pianic2/homeedge-ai-platform/docs/evidence/IHAP-52/summaries/README.md

# IHAP-52 Sanitized Validation Summaries

This directory is reserved for reviewed aggregate summaries generated from central-node validation runs.

Raw harness output under `tools/hardware-validation/ihap-52-central-node/runs/` remains local and ignored by Git.

A public summary may be added only after checking that it does not expose Wi-Fi credentials, SSIDs, MAC addresses, private IP addresses, hostnames, usernames or unnecessary local paths.

A summary may report:

- device family/model;
- architecture, logical CPU count and RAM capacity;
- storage capacity and microSD application class;
- Wi-Fi gate pass/fail without private addressing;
- PSU electrical rating and pass/fail disposition;
- temperature aggregates and throttling/undervoltage flags;
- stress duration and worker result;
- overall automated gate;
- manual cooling/enclosure configuration;
- explicit `[UNVALIDATED]` boundaries.

The 2026-09-05 pre-flight is not yet a publishable final validation summary because the full stress phase did not execute. It is retained as task evidence in the IHAP-52 evidence index and Jira.

A passing summary supports only the declared IHAP-52 validation envelope. It does not prove production readiness, final application sizing, microSD endurance/retention or AI acceleration.
