pianic2/homeedge-ai-platform/docs/product/product-vision.md

# Product Vision, MVP Boundaries and Glossary

**Issue:** IHAP-11 — S0-002 — Product Vision, MVP Boundaries and Glossary  
**Project:** [ITS] [EDGE] HomeEdge AI Platform  
**Document type:** Product foundation / governance documentation  
**Status:** Active product foundation — updated through accepted ADRs  
**Last controlled MVP update:** 2026-08-31 — ADR-0004 Local Status Display  
**Source of truth:** This versioned GitHub document is the technical source of truth for the Product Vision, MVP boundaries, and initial glossary until superseded by a later reviewed change.

<!--
AI_AGENT_METADATA:
  issue: IHAP-11
  related_issues:
    - IHAP-15
    - IHAP-53
  document_type: product_foundation
  source_of_truth: github_versioned_documentation
  task_scope: documentation_governance_only
  runtime_changes_allowed: false
  firmware_changes_allowed: false
  backend_changes_allowed: false
  mobile_changes_allowed: false
  production_ready_claims_allowed: false
  unvalidated_claim_marker: "[UNVALIDATED]"
  mvp_firmware_node: "firmware/room-env-node/"
  mvp_node_semantics: "generic_room_door_node"
  mvp_physical_positioning: "near_room_door"
  mvp_includes:
    - temperature_collection
    - humidity_collection
    - local_presence_detection
    - door_open_closed_state
    - local_status_display
    - http_json_event_direction
    - minimal_event_schema_direction
    - documentation_governance
  accepted_local_display_adr: ADR-0004
  local_display_runtime_integration_status: unvalidated_until_final_room_node_implementation
  mvp_excludes:
    - raw_audio_collection
    - individual_presence_tracking
    - behavioral_history_tracking
    - person_identification
    - window_sensor_scope
    - 220v_automation
    - esp32_direct_kafka_producer
    - production_grade_security_certification
    - commercial_claims
    - safety_critical_claims
  service_boundaries_target_only:
    - services/ingestion/
    - services/device-registry/
    - services/read-model/
    - services/ai-insight/
  data_classification_boundary:
    canonical_section: "4.4 Data Classification and Privacy Boundaries"
    mvp_data:
      - temperature
      - humidity
      - local_non_identifying_presence_state
      - door_open_closed_telemetry
    technical_metadata:
      - timestamp
      - device_node_id
      - room_id
      - firmware_version
      - ip_network_metadata
    future_or_out_of_mvp:
      - window_sensor_scope
      - advanced_presence_analytics
    blocked_data:
      - raw_audio
      - person_identification
      - individual_presence_tracking
      - behavioral_history
      - routine_profiling
    stakeholder_exposure:
      raw_audio: blocked
      identity_data: blocked
      behavioral_history: blocked
      private_network_metadata: redact_or_omit
      door_state: telemetry_only
      presence_state: local_non_identifying_only
  review_policy:
    - do_not_close_jira_without_project_owner_approval
    - keep_mvp_future_out_of_mvp_target_distinction
    - do_not_overstate_runtime_maturity

HIDDEN_ANTI_REGRESSION_RULES:
  - This document must not contradict the repository skeleton introduced by IHAP-10.
  - The only firmware node in the MVP is firmware/room-env-node/.
  - firmware/room-env-node/ represents the first generic room/door node positioned near the room door.
  - The MVP includes temperature, humidity, local non-identifying presence detection, door open/closed state, and the local status display capability accepted by ADR-0004.
  - ADR-0004 does not imply that final room-node display firmware, final pinout, quantitative power, enclosure mechanics or BOM propagation are already complete.
  - The local display is read-only, compact status/debug UI; do not turn it into a terminal, touch UI, identity/history surface, or alarm/security interface.
  - No dedicated status LED is an MVP requirement when the accepted local display provides local status indication.
  - The four backend directories remain target service boundaries, not proof of completed production services.
  - Kafka direct production from ESP32 remains OUT OF MVP.
  - Backend-side Kafka/event streaming remains FUTURE unless a later ADR and implementation task validate it.
  - Raw audio collection remains OUT OF MVP.
  - Local, non-identifying presence detection is allowed inside the MVP.
  - Individual presence tracking, behavioral history, identity inference, and routine profiling remain OUT OF MVP.
  - Door open/closed state is allowed inside the MVP as telemetry only.
  - Door state must not be presented as certified access control, alarm-grade intrusion detection, or safety-critical security evidence.
  - Window sensors remain FUTURE and OUT OF MVP unless changed by ADR.
  - 220V automation remains OUT OF MVP.
  - Mobile monitoring is a target direction unless supported by implementation evidence.
  - AI insight is a target/future service boundary unless supported by implementation evidence.
  - Stakeholder reports must not contain sensitive data, raw personal telemetry, raw audio, behavioral tracking, or unsupported production/safety/commercial claims.
  - Any unproven claim must be marked as [UNVALIDATED].
  - Documentation must distinguish clearly between MVP, FUTURE, OUT OF MVP, and TARGET.
  - Jira must track status, evidence, decisions, and review state.
  - GitHub must remain the source of truth for versioned technical documentation.

HIDDEN_EVIDENCE_EXPECTATIONS:
  - A GitHub branch dedicated to the active task.
  - A pull request linked to the active Jira issue.
  - This versioned document under docs/product/product-vision.md.
  - A Jira comment linking the PR and summarizing the documentation scope.
  - Jira status moved to review after PR creation or Project Owner instruction.
  - No transition to completed until explicit project owner approval.
-->

---

## 1. Product Snapshot

HomeEdge AI Platform is an educational, portfolio-grade smart home platform built around a first edge node, backend service boundaries, mobile monitoring, and source-of-truth documentation.

The first MVP node is a **generic room/door node** positioned near the room door.

The MVP focuses on a small, reviewable smart home vertical slice:

- room temperature;
- room humidity;
- local non-identifying presence detection;
- room door open/closed state;
- a compact read-only local status display for user/maintenance visibility, accepted by ADR-0004;
- HTTP/JSON event direction toward ingestion;
- documented backend service boundaries;
- governance through GitHub and Jira.

The local display capability is part of the MVP product boundary. The tested 0.96-inch-class 128×64 monochrome I2C profile and owned specimen evidence are defined by ADR-0004. Final integration into `firmware/room-env-node/`, final pins, quantitative power behavior, enclosure mechanics and definitive BOM propagation remain separate work and must not be inferred from this Product Vision update.

The MVP does **not** include person tracking, behavioral history, raw audio collection, certified access control, alarm-grade intrusion detection, 220V automation, or direct Kafka production from ESP32.

---

## 2. Document Control

This document defines the product framing for HomeEdge AI Platform and is updated by reviewed Product Owner decisions and accepted ADRs.

It is intentionally limited to product documentation and governance. It does **not** introduce firmware, backend, mobile, infrastructure, CI/CD, cloud, Kafka, AI runtime, or production implementation by itself.

### 2.1 Scope of this document

Included:

- Product Vision.
- MVP boundaries.
- FUTURE scope.
- OUT OF MVP scope.
- Initial glossary.

Excluded:

- Runtime implementation.
- Firmware implementation changes.
- Backend service implementation.
- Mobile app implementation.
- Production-readiness claims.
- Safety-critical claims.
- Commercial claims.

### 2.2 Claim policy

Any capability that is not implemented, tested, and supported by runtime evidence must be marked as `[UNVALIDATED]`.

An accepted architectural/product requirement may be part of the MVP boundary before final runtime integration, but its implementation maturity must remain explicit. ADR-0004 therefore accepts the local-display capability/profile while final room-node integration remains `[UNVALIDATED]` until implementation evidence exists.

A statement may describe a **TARGET** architecture only when it is explicitly framed as target, planned, or future work.

---

## 3. Product Vision

### 3.1 What HomeEdge AI Platform is

HomeEdge AI Platform is an educational, portfolio-grade smart home platform that connects edge devices, backend services, mobile monitoring, structured documentation, and an AI-ready insight layer.

The platform is designed around an edge-first architecture:

```text
Edge Nodes -> Backend Services -> Mobile Dashboard -> AI-ready Insights
```

At Sprint 0, this is a product and architecture direction, not proof that all runtime components already exist.

### 3.2 Why it exists

HomeEdge exists to create a coherent end-to-end engineering project suitable for the ITS context and for a technical portfolio.

The project connects multiple disciplines in one traceable system:

- embedded firmware on ESP32-class devices;
- sensor-based smart home telemetry;
- compact local device status/debug visibility;
- HTTP/JSON event ingestion;
- backend service boundaries;
- mobile-first monitoring;
- documentation as source of truth;
- governance through Jira, GitHub, and review evidence;
- AI-ready data interpretation as a later architectural target.

### 3.3 Problem it solves

HomeEdge addresses the problem of building a smart home system in a controlled, incremental, and reviewable way.

Instead of starting from a broad and ambiguous smart home vision, the project narrows the first vertical slice to a single generic room/door node and a minimal telemetry flow.

The project solves these early engineering problems:

- making hardware, firmware, backend, mobile, and documentation boundaries explicit;
- preventing uncontrolled scope expansion;
- avoiding unverified production-ready claims;
- keeping stakeholder visibility high;
- documenting what is implemented, what is targeted, and what is explicitly out of scope;
- creating a project structure that can scale without hiding current maturity.

### 3.4 Educational and portfolio value

HomeEdge is valuable as a learning and portfolio project because it demonstrates how to model a real platform from the beginning, not only how to write isolated code.

It shows:

- product thinking;
- architectural decomposition;
- embedded-to-cloud reasoning;
- source-of-truth documentation;
- issue-driven delivery;
- pull-request evidence;
- anti-regression governance;
- explicit MVP scoping;
- clear distinction between implemented features and target architecture.

This makes the project readable for ITS stakeholders, reviewers, recruiters, and future collaborators.

### 3.5 Technical value

HomeEdge is technically valuable because it is structured as a scalable platform rather than a single prototype script.

The main technical axes are:

- **Edge devices:** ESP32-class nodes collecting room-level signals and exposing a compact local status/debug surface.
- **Backend services:** target service boundaries for ingestion, device registry, read model, and AI insight.
- **Mobile monitoring:** mobile-first dashboard direction for telemetry and device health visibility.
- **AI-ready insight layer:** future service boundary for deriving insights from validated data.
- **Governance:** Jira for workflow and evidence, GitHub for versioned technical source of truth, and PR reviews for change validation.

At Sprint 0, these axes define direction and boundaries. They do not imply that every component is implemented.

---

## 4. MVP Boundaries

### 4.1 MVP definition

The MVP is the smallest reviewable vertical slice of HomeEdge.

It must prove the platform direction without expanding into high-risk or unvalidated smart home automation features.

The MVP is centered on one firmware node:

```text
firmware/room-env-node/
```

This node is the first generic room/door node of the smart home platform. It is assumed to be positioned near the room door and is responsible for collecting minimal room-level signals.

In the MVP, the node may collect:

- temperature;
- humidity;
- local non-identifying presence state;
- door open/closed state.

The MVP node also includes a **compact read-only local status display capability** accepted by ADR-0004. The accepted display profile is 0.96-inch-class, 128×64, monochrome OLED over I2C. Final room-node rendering/driver integration remains `[UNVALIDATED]` until implemented and tested outside the IHAP-53 validation harness.

No other firmware node is part of the MVP unless a later ADR explicitly changes this boundary.

### 4.2 MVP included

The MVP includes the following scope:

| Area | MVP scope | Status framing |
|---|---|---|
| Firmware node | One generic Room/Door Environment Node under `firmware/room-env-node/` | MVP |
| Physical placement | Node positioned near the room door | MVP assumption |
| Environment telemetry | Temperature and humidity collection | MVP |
| Local presence | Local presence detection as a boolean or state signal, without identity, behavioral history, or individual tracking | MVP |
| Door state | Door open/closed state detection | MVP |
| Local status display | Compact read-only 0.96-inch-class 128×64 monochrome I2C status/debug display; healthy UI shows room label, temperature, humidity, presence and door state; no dedicated status LED requirement | MVP capability accepted by ADR-0004; final room-node firmware/pinout/power/enclosure integration remains `[UNVALIDATED]` |
| Transport | HTTP/JSON event sent toward ingestion backend | MVP target until implemented and verified |
| Event model | Minimal event schema for room environment, presence state, and door state | MVP target until implemented and verified |
| Backend | Ingestion boundary as target service area | TARGET |
| Device registry | Device identity/metadata boundary as target service area | TARGET |
| Read model | Query/read-oriented boundary as target service area | TARGET |
| AI insight | AI-ready insight boundary as target service area | TARGET / FUTURE |
| Mobile dashboard | Mobile monitoring documented as target | TARGET |
| Documentation | GitHub versioned documentation as source of truth | MVP governance |
| Jira governance | Jira comments/status/evidence for task tracking | MVP governance |

Presence detection in the MVP means detecting whether presence is currently observed in a room-level context.

Presence detection does **not** mean tracking people, identifying people, storing behavioral history, profiling routines, or producing safety-critical occupancy guarantees.

Door state detection in the MVP means detecting whether the room door is open or closed.

Door state detection does **not** mean access control, intrusion certification, alarm-grade security, or safety-critical monitoring.

The local display may present only current permitted room-level status and compact maintenance diagnostics. It must not expose identity, behavioral/occupancy history, credentials, SSID, access-control/alarm semantics or other data outside the accepted privacy boundary.

### 4.3 Minimal event direction

The MVP event direction is HTTP/JSON from `room-env-node` toward an ingestion backend.

A minimal room environment event may include fields such as:

```json
{
  "event_type": "room.environment.sampled",
  "device_id": "room-env-01",
  "timestamp": "2026-07-07T00:00:00Z",
  "temperature_c": 24.5,
  "humidity_percent": 55.0,
  "presence_detected": false,
  "door_open": false,
  "firmware_version": "0.0.0-unvalidated"
}
```

This schema is directional and must remain `[UNVALIDATED]` until the schema is formally versioned, implemented, and tested.

The `presence_detected` field represents a local, non-identifying room-level state. It must not be interpreted as identity, person tracking, behavioral profiling, or safety-critical occupancy evidence.

The `door_open` field represents the local open/closed state of the room door. It must not be interpreted as certified access control, intrusion detection, or safety-critical security evidence.

### 4.4 Data Classification and Privacy Boundaries

The MVP uses minimal room-level telemetry. Data must stay classified by purpose, privacy boundary, and stakeholder exposure.

| Data / signal | Classification | MVP status | Privacy boundary | Stakeholder exposure |
|---|---|---|---|---|
| Temperature | Room telemetry | MVP | Non-identifying room-level signal. | Show allowed. |
| Humidity | Room telemetry | MVP | Non-identifying room-level signal. | Show allowed. |
| Presence detected | Local state telemetry | MVP | Local, non-identifying state only; no identity, individual tracking, behavioral history, or routine profiling. | Show only as generic room state. |
| Door open/closed | Local state telemetry | MVP | Telemetry only; not access control, antifurto, alarm-grade, safety-critical, or security-certified evidence. | Show only as telemetry. |
| Timestamp | Technical metadata | MVP / TARGET depending on schema evidence | Can support inference if retained, correlated, or shown with other signals. | Show only when needed; redact or aggregate where appropriate. |
| Device/node id | Technical metadata | MVP / TARGET depending on schema evidence | Must not expose sensitive domestic topology or private installation details. | Redact or omit unless required for review. |
| Room id | Technical metadata | MVP / TARGET depending on schema evidence | Must remain generic; no private address or precise domestic location. | Generic labels only. |
| Firmware version | Technical metadata | MVP / TARGET depending on schema evidence | Useful for evidence, but not a privacy or security guarantee. | Show allowed when useful. |
| IP/network metadata | Technical metadata | OUT of stakeholder view | Sensitive domestic/infrastructure detail. | Redact or omit. |
| Raw audio | Sensitive raw signal | OUT OF MVP | Not collected in MVP. | Blocked. |
| Person identification | Identity data | OUT OF MVP | Not allowed. | Blocked. |
| Individual presence tracking | Behavioral or identity-linked data | OUT OF MVP | Not allowed. | Blocked. |
| Behavioral history / routine profiling | Behavioral data | OUT OF MVP | Not allowed. | Blocked. |
| Window sensors | Opening telemetry | FUTURE / OUT OF current MVP | Not part of the current room/door node scope. | Do not imply MVP delivery. |

The accepted local display does not create a new class of telemetry. It may expose only current values/states permitted by this table plus compact maintenance diagnostics allowed by ADR-0004. Normal display content must omit SSID, credentials and behavioral history; private network metadata remains excluded from ordinary stakeholder/user display.

The table does not validate runtime behavior. Event fields, service boundaries, mobile views, AI insight, storage behavior, and final room-node display integration remain `[UNVALIDATED]` until implementation and test evidence exist.

### 4.5 MVP acceptance boundary

The MVP must remain understandable without requiring any of the following:

- multiple hardware node types;
- raw audio collection;
- individual presence tracking;
- behavioral presence history;
- person identification;
- window detection;
- certified access control;
- alarm-grade intrusion detection;
- 220V automation;
- direct Kafka production from ESP32;
- cloud deployment;
- production-grade security certification;
- commercial or safety-critical positioning.

The accepted local status display is part of the MVP and is therefore not an optional FUTURE feature. Its presence must not be used to imply final firmware integration, production maturity, quantitative autonomy, certified enclosure suitability or security/alarm semantics.

---

## 5. FUTURE Scope

The following items are intentionally future scope. They may be explored later only through explicit tasks, ADRs, risk assessments, and review evidence.

| Area | FUTURE item | Notes |
|---|---|---|
| Presence | Advanced presence radar features | Basic local presence detection is MVP; identity, tracking, behavioral history, room-to-room movement analysis, and advanced presence analytics are not MVP. |
| Openings | Window sensors and multi-opening topology | Door open/closed state for the first room/door node is MVP; window sensors and multi-opening modeling are FUTURE. |
| Audio-derived signals | Noise detection derived from local processing | Raw audio collection remains OUT OF MVP. |
| Automation | Smart home automations | Requires safety and risk review. |
| AI | Advanced AI insight generation | Requires validated data and clear privacy boundaries. |
| Event streaming | Kafka on backend/event streaming side | Backend-side target only, not ESP32 direct producer in MVP. |
| DevOps | More complete CI/CD | Future hardening task. |
| Deployment | Cloud deployment | Future deployment milestone. |
| Mobile | Full mobile dashboard implementation | Target beyond initial documentation unless separately implemented. |

FUTURE means planned or possible later work. It does not mean implemented.

---

## 6. OUT OF MVP Scope

The following items are explicitly out of the MVP and must not be implied as delivered by Sprint 0 documentation.

| Item | Reason |
|---|---|
| Raw audio collection | Privacy risk and not needed for the first telemetry vertical slice. |
| Individual presence tracking | OUT OF MVP. The MVP may detect local presence state, but must not identify people, track individuals, store behavioral history, or profile routines. |
| Behavioral presence history | OUT OF MVP. Presence events must not become a person-level movement log or routine inference system in the MVP. |
| Window sensors in MVP | OUT OF MVP. The first MVP node may detect the room door open/closed state, but window sensors are future scope. |
| Certified access control | OUT OF MVP. Door open/closed state is telemetry only, not an access-control or alarm-grade security feature. |
| Alarm-grade intrusion detection | OUT OF MVP. Door state and presence state must not be presented as certified intrusion detection. |
| 220V automation | Safety risk and requires dedicated electrical/security review. |
| Production-grade security/certification | Not implemented or verified in Sprint 0. |
| Kafka client directly on ESP32 | Too heavy and outside the MVP boundary; backend event streaming may be future scope. |
| Commercial claims | Project is educational/portfolio-oriented unless later validated otherwise. |
| Safety-critical claims | No safety-critical guarantees are provided. |
| Full AI automation | AI insight is a target boundary, not a validated runtime capability in Sprint 0. |

---

## 7. Target Service Boundaries

The repository skeleton defines four backend service boundaries:

```text
services/ingestion/
services/device-registry/
services/read-model/
services/ai-insight/
```

These are **target service boundaries**.

They do not prove that production-ready services exist. They define where backend responsibilities should be modeled as the platform evolves.

### 7.1 Ingestion boundary

The ingestion boundary is responsible for receiving, validating, and accepting telemetry events from edge nodes.

At Sprint 0, this is a target boundary unless implementation evidence exists in a later task.

### 7.2 Device Registry boundary

The device registry boundary is responsible for device identity, metadata, and lifecycle state.

At Sprint 0, this is a target boundary unless implementation evidence exists in a later task.

### 7.3 Read Model boundary

The read model boundary is responsible for query-oriented representations of data used by dashboards, APIs, or monitoring views.

At Sprint 0, this is a target boundary unless implementation evidence exists in a later task.

### 7.4 AI Insight boundary

The AI insight boundary is responsible for future interpretation, classification, summarization, anomaly detection, or insight generation from validated data.

At Sprint 0, this is a target/future boundary, not a validated AI runtime.

---

## 8. Glossary

| Term | Definition |
|---|---|
| Edge Node | A physical embedded device near the environment being observed. In this project, edge nodes are expected to use ESP32-class hardware unless changed by ADR. |
| Generic Room/Door Node | The first MVP smart home node placed near a room door. It collects minimal room environment data, local presence state, door open/closed state, and includes the accepted local status display capability. |
| Room Environment Node | The MVP firmware node located at `firmware/room-env-node/`. In the MVP, it acts as a generic room/door node responsible for temperature, humidity, local presence detection, door open/closed state, and the local status display capability accepted by ADR-0004. |
| Local Status Display | The read-only compact status/debug display accepted by ADR-0004 for the reference MVP node. Reference profile: 0.96-inch-class, 128×64, monochrome OLED, I2C. Final product pinout, power policy, enclosure and definitive BOM remain separate follow-up work. |
| Event | A structured record describing something observed or produced by the system, such as a room environment sample. |
| Door State | A local telemetry signal indicating whether the room door is open or closed. It is allowed in the MVP as a non-certified state signal. |
| Presence Detection | A local, non-identifying room-level signal indicating whether presence is currently detected. It is allowed in the MVP only as a minimal state signal. |
| Presence Tracking | Person-level, historical, behavioral, or identity-linked tracking of presence over time. This is OUT OF MVP. |
| Ingestion | The backend boundary responsible for receiving and validating incoming events. |
| Device Registry | The backend boundary responsible for device identity, metadata, ownership, lifecycle, and known-device state. |
| Read Model | A query-optimized representation of data used by dashboards, APIs, or monitoring views. |
| AI Insight | A future or target capability that derives higher-level interpretation from validated data. It is not a Sprint 0 runtime claim. |
| Source of Truth | The authoritative place where a technical decision, boundary, or project fact is maintained. For versioned technical documentation, this is GitHub unless explicitly superseded. |
| ADR | Architecture Decision Record. A reviewed document that captures an architectural decision, context, consequences, and alternatives. |
| MVP | Minimum Viable Product. The smallest coherent and reviewable vertical slice of the platform. |
| FUTURE | A planned or possible later capability. It is not implemented unless separate evidence proves it. |
| OUT OF MVP | Explicitly excluded from the current MVP scope. These items must not be implied as delivered. |
| TARGET | A documented architectural direction or service boundary. It is not proof of implementation. |
| `[UNVALIDATED]` | Marker for a claim, capability, schema, flow, or assumption that has not yet been implemented, tested, and supported by runtime evidence. |
| Stakeholder Report | A concise status report for stakeholders, such as ITS professors, that communicates progress, risks, evidence, and next steps without leaking sensitive data or making unsupported claims. |
| Runtime Evidence | Concrete evidence from running software or hardware, such as logs, tests, screenshots, traces, build outputs, or verified API responses. |
