pianic2/homeedge-ai-platform/docs/evidence/IHAP-55/review-summary.md

# IHAP-55 pre-fabrication review checkpoint — 2026-09-13

**Readiness: HOLD.** This is a technical checkpoint in existing branch `ihap-55-integrated-modular-edge-pcb` and draft PR #37, not a fabrication or reference-implementation approval.

The 2026-09-12 review compared the accepted ADR-0001/0002/0003/0004/0005/0007 and IHAP-50 connection matrix with the revision-A JSON contract and copied firmware. GPIO0/1/3/4/5/6/7/10, USB GPIO18/19, reserved strapping GPIO2/8/9, optional UART0 GPIO20/21, connector logical pin order, DHT11/BME280 alternatives, radar receive-only 256000 baud and MC-38 10 kΩ/1 kΩ/DNP 100 nF remain represented. No audio GPIO, ADC, connector or power allocation was added. The IHAP-50 firmware main source was identical before the IHAP-55 ADC/command additions; the existing integrated sample stream was retained.

Software gate evidence: 28/28 behavioral cases and 12/12 host tests passed; ESP-IDF v6.0.1 compiled the ESP32-C3/4 MB/USB Serial-JTAG firmware. The TLA2024 four-channel path is initialized, read, range-checked and serialized in the command response, but has no physical-board validation.

The existing PR #37 was updated to commit `2926a9019cbc9f0fd4081286352928bc6102162e` on 2026-09-13. [GitHub Actions run 34757325971](https://github.com/pianic2/homeedge-ai-platform/actions/runs/34757325971) completed successfully: `contract-and-host` passed; `kicad-erc-drc` job completed but explicitly skipped KiCad installation, ERC and DRC because neither EDA source exists. This is CI software-gate success, **not** an ERC/DRC PASS. Later evidence commits require a fresh CI check at their own HEAD.

Two technical failures prevent an EDA/fabrication-ready claim: (1) the passive board-health ADC dividers can drive AIN above VDD+0.3 V while SYS_3V3 is absent; (2) the vendor PSpice experiments under ngspice 44.2 did not produce plausible output voltages, so no switching model validates dynamic rail performance. MP2636 protection/NTC, reverse-cell prevention, exact passives and module pull-ups are additional open circuit items. No native schematic/PCB, ERC, preliminary envelope or DRC exists at this checkpoint.

The Accepted ADR-0007 baseline remains unchanged. IHAP-56's `RT-R012-01` and `RT-R013-01` remain Proposed/Pending Evidence. No procurement, fabrication or merge was performed. Project Owner gates are deferred until a technically reviewable board and IHAP-51 mechanical feedback exist.
