pianic2/homeedge-ai-platform/docs/evidence/IHAP-49/ihap-56-post-merge-reconciliation.md

# IHAP-56 Post-Merge Lifecycle Reconciliation

**Created:** 2026-09-11  
**Consumer:** IHAP-55 startup / downstream hardware work  
**Scope:** workflow/lifecycle reconciliation only

## Authoritative current state

- ADR-0007 / PR #34 baseline: **Accepted**.
- IHAP-56: **Completata**.
- PR #35: **merged 2026-09-10** as `629ff78965a20481cf68954d6bcb8ac865fc27c2`.
- IHAP-55: **In corso** from 2026-09-11 under explicit Project Owner authorization.
- RT-R012-01: **Proposed**.
- RT-R013-01: **Proposed**.
- Residual risk acceptance: **not granted**.
- Physical effectiveness: `[UNVALIDATED]`.

## Stale-workflow supersession

PR #35 intentionally contained pre-merge review gates. After its authorized merge, several copied status sentences remained in the IHAP-49 evidence package.

For **workflow/lifecycle interpretation only**, this document and `status.md` supersede residual statements in the following files that say PR #35 is not merged, IHAP-56 is still in review, or IHAP-55 remains blocked by IHAP-56:

- `README.md`;
- `review-summary.md`;
- `validation-plan.md`;
- `downstream-contracts.md`;
- `custom-pcb-power-contract.md`.

Those stale gate sentences are historical review snapshots, not active blockers.

## Technical anti-regression boundary

This reconciliation does **not** supersede technical requirements in those files. In particular it does not:

- promote any Proposed IHAP-56 control to Accepted;
- approve RT-R012-01 or RT-R013-01;
- extend accepted quantitative ownership to ADR-0003;
- accept residual risk;
- validate cell-side interruption, NTC fault handling, numeric thermal/low-voltage policy, V13/V14/V15, strengthened V7/V8/V9, or quantified backfeed criteria;
- prove PCB rail, transfer, battery, thermal, RF or enclosure behavior;
- authorize procurement or fabrication.

Accepted PR #34 / ADR-0007 architecture and the Accepted IHAP-50 interconnect contract remain unchanged.

## IHAP-51 interlock

The old one-way model `IHAP-51 blocks IHAP-55` is stale. Current execution is iterative:

1. IHAP-55 produces preliminary board outline, mounting-hole candidates, connector placement, ESP32 antenna keepout and major keepouts.
2. IHAP-51 reviews enclosure fit, access, routing, placement and strain relief.
3. Mechanical feedback returns to IHAP-55.
4. Final PCB layout is frozen only after that feedback loop.

The legacy Jira Blocks relation is recorded as stale in Jira comments because the available Atlassian integration does not expose issue-link deletion. It must not be interpreted as an active blocker while IHAP-55 is In corso.
