pianic2/homeedge-ai-platform/docs/evidence/IHAP-49/review-summary.md

# IHAP-49 — Review and Acceptance Summary

**Post-merge lifecycle reconciliation:** 2026-09-11.

## Accepted baseline

Project Owner approval on 2026-09-07 applies to ADR-0007 / PR #34: regulated 5 V USB-C normal source; LG INR18650-MJ1 backup only; one custom modular core PCB; MP2636 first direction plus downstream 5 V regulation/reviewed equivalent; 5 V SYS 4.75–5.25 V with >=0.5 A continuous **across accepted battery and valid USB-input ranges** and >=1 A headroom; USB priority/takeover/backfeed prohibition; no-reset target `[UNVALIDATED]`; NTC monitoring; electrical/mechanical reverse-insertion prevention; quantitative ownership transfer from ADR-0001/0002/0004/0005.

## Proposed IHAP-56 overlay

RT-R012-01 / RT-R013-01 remain **Proposed**. The overlay contains source-side over-current + upstream residual handling, NTC fault-state verification, thermal/Tj method, ILIM/V14, component-derived 3.3 V criteria, bidirectional V7, high/mid/valid-low V8/V9 with cutoff margin/quantified backfeed/zero-reset restoration, numeric V10, V13 installed path, V15 USB absent/present and the ADR-0003 ownership extension. None inherits PR #34 approval or approval from PR #35 merge.

## Global closure sweep and final disposition

`ihap-56-closure-matrix.md` maps material requirements to Accepted/Proposed state, owner, downstream consumer, validation evidence and approval boundary. The 2026-09-09 sweep reconciled all 16 files changed by PR #35 and addressed the latest review findings together.

Historical review provenance:

- Codex pass `fa2f3842c9`: 8 findings, remediated.
- Codex pass `214eac063c`: 6 findings, remediated.
- Later Codex pass: 8 findings addressed by the global closure sweep.
- Project Owner subsequently authorized the remediation closure.
- PR #35 merged on **2026-09-10** as `629ff78965a20481cf68954d6bcb8ac865fc27c2`.
- Jira IHAP-56 is **Completata**.
- The IHAP-56 remediation dependency on IHAP-55 is therefore **cleared**.
- IHAP-55 entered **In corso** on 2026-09-11 under explicit Project Owner authorization.

## Approval boundary preserved

Closing IHAP-56 and merging PR #35 do **not** approve RT-R012-01, RT-R013-01, the Proposed ADR-0007 amendment detail, residual risk, or any physical implementation claim. Those items remain Proposed/Pending Evidence until their explicit downstream gates are satisfied.

Any residual pre-merge sentence elsewhere in the IHAP-49 evidence package stating that PR #35 or IHAP-55 `remains blocked` is a historical workflow snapshot and is superseded by `status.md` and `ihap-56-post-merge-reconciliation.md` for lifecycle interpretation.
