pianic2/homeedge-ai-platform/docs/evidence/IHAP-50/IHAP50-PRECISION-01-summary.md

# IHAP50-PRECISION-01 — IHAP-50 integrated gate

- Profile: `precision`
- Commit: `6e1200afe15492c283edc6afd39059b2947b7fae`
- Result: **PASS**
- Captured UTC: `2026-09-11T09:49:02.310431+00:00`

## Checks

- [x] `record_type`
- [x] `firmware`
- [x] `pins`
- [x] `adc_spare`
- [x] `digital_spare`
- [x] `radar_service_tx_disabled`
- [x] `profile`
- [x] `bme_presence`
- [x] `oled_visual_transfer`
- [x] `sample_count`
- [x] `oled_reliability`
- [x] `radar_freshness`
- [x] `radar_valid_frames`
- [x] `radar_no_invalid_frames`
- [x] `profile_consistency`
- [x] `bme_present`
- [x] `bme280_reliability`
- [x] `bme280_identity`
- [x] `operator_oled_visual_confirmation`
- [x] `operator_connector_polarity_review`

## Errors

- None

## Evidence boundary

Integrated prototype interconnect evidence only; not final PCB/power/certification evidence.

Raw serial data stays local under `runs/` and must not be committed by default.
