pianic2/homeedge-ai-platform/docs/evidence/IHAP-50/IHAP50-STANDARD-11-summary.md

# IHAP50-STANDARD-11 — IHAP-50 integrated gate

- Profile: `standard`
- Commit: `6e1200afe15492c283edc6afd39059b2947b7fae`
- Result: **PASS**
- Captured UTC: `2026-09-11T09:42:48.491934+00:00`

## Checks

- [x] `record_type`
- [x] `firmware`
- [x] `pins`
- [x] `adc_spare`
- [x] `digital_spare`
- [x] `radar_service_tx_disabled`
- [x] `profile`
- [x] `bme_presence`
- [x] `oled_visual_transfer`
- [x] `sample_count`
- [x] `oled_reliability`
- [x] `radar_freshness`
- [x] `radar_valid_frames`
- [x] `radar_no_invalid_frames`
- [x] `profile_consistency`
- [x] `bme_absent`
- [x] `dht11_reliability`
- [x] `open_sample_count`
- [x] `open_door_raw`
- [x] `open_radar_alive`
- [x] `open_oled_alive`
- [x] `closed_sample_count`
- [x] `closed_door_raw`
- [x] `closed_radar_alive`
- [x] `closed_oled_alive`
- [x] `disconnected_sample_count`
- [x] `disconnected_door_raw`
- [x] `disconnected_radar_alive`
- [x] `disconnected_oled_alive`
- [x] `operator_oled_visual_confirmation`
- [x] `operator_connector_polarity_review`

## Errors

- None

## Evidence boundary

Integrated prototype interconnect evidence only; not final PCB/power/certification evidence.

Raw serial data stays local under `runs/` and must not be committed by default.
