pianic2/homeedge-ai-platform/docs/evidence/IHAP-48/final-review-summary.md

# IHAP-48 — Final Specialist Review Summary

**Issue:** IHAP-48 — Audio Hardware Disposition — GY-MAX4466  
**PR:** #32  
**Reviewed decision-content head:** `9ad715f725f72eebd0dcea68eebacca95f715ef6`  
**Review date:** 2026-08-31  
**Project Owner decision:** remove GY-MAX4466 from reference MVP; retain as FUTURE inventory only

---

## Scope reviewed

The review covers:

- `docs/architecture/ihap-48-audio-hardware-disposition.md`;
- `docs/evidence/IHAP-48/README.md`;
- the IHAP-48 navigation change in `docs/README.md`;
- compatibility with current `main` after PR #31 / ADR-0004;
- Product Vision raw-audio and profiling boundaries;
- ADR-0001 compute constraints;
- ADR-0004 local-display dependency;
- R-002 event-payload leakage boundary;
- R-007 AI inference/profiling boundary;
- provisional IHAP-17 `EDGE_INSTALLED_DISABLED` classification as downstream work only;
- Analog Devices primary documentation for the MAX4466 IC family.

No firmware, runtime, downstream task branch, ADR or Product Vision file is changed by PR #32.

---

## Review results

| Perspective | Result | Review conclusion |
|---|---|---|
| Security & Privacy | **PASS** | Physical removal is the strongest proportionate least-privilege control. Raw audio, speech/voice recognition, identity, individual tracking, behavioral history and routine profiling remain blocked. No latent powered audio surface is retained. |
| Stakeholder Clarity | **PASS** | The record clearly distinguishes owned inventory from reference-MVP inclusion. It explicitly states that audio is a genuinely considered FUTURE addition while remaining outside the MVP and requiring separate approval. |
| Hardware Compatibility | **PASS** | Reference-MVP audio allocation is unambiguously zero for ADC/GPIO, power, wiring, connectors, aperture/mounting and firmware. No undocumented module-level pinout/current/gain characteristic is used to justify the decision. |
| Architecture Regression | **PASS** | Product Vision is not expanded, ADR-0001/0002/0004 are not reopened, no audio runtime capability is reserved, and no parallel IHAP-46/47/52 work is modified. ADR-not-required is proportionate because the component is removed rather than retained as a stable dependency. |
| Testing & Evidence | **PASS** | The selected state is structural absence, so an audio functional harness would not increase confidence in the disposition. Evidence is sufficient to verify the boundary and primary IC-family purpose; exact owned-module behavior remains explicitly unclaimed. |
| Cost Governance | **PASS** | Sunk-cost reasoning is rejected. Owned modules remain historical/FUTURE inventory and must not contribute to required reference-node replication cost. IHAP-17 receives a reference quantity of zero as downstream handoff. |
| Source of Truth | **PASS** | GitHub contains the durable technical disposition; Jira owns workflow/decision evidence; Confluence may summarize/link only. The record is navigated from `docs/README.md` without creating a new canonical governance-policy path. |

Final severity gate for changes introduced by IHAP-48:

```text
BLOCKER = 0
MAJOR   = 0
```

---

## Evidence sufficiency

### Accepted evidence

- current Product Vision explicitly excludes raw audio from MVP;
- current ADR-0001 does not authorize audio acquisition or audio-derived runtime behavior;
- current ADR-0004 establishes the accepted local-display dependency without introducing audio scope;
- R-002 and R-007 preserve privacy/inference boundaries;
- Analog Devices documents MAX4466 as a microphone-preamplifier IC family;
- Project Owner explicitly selected complete physical removal from the reference MVP;
- PR #32 contains no firmware/runtime implementation.

### Deliberately not required

The following are not required for a removal decision and remain unclaimed:

- exact GY-MAX4466 module pinout;
- exact module current draw;
- microphone capsule type;
- gain-network values;
- waveform quality;
- ESP32 ADC performance with the module;
- speech or derived-signal feasibility;
- seller/lot reproducibility.

A specimen photograph can be added later as inventory-identification evidence but is not required to prove that the reference MVP excludes the component.

---

## ADR necessity review

**PASS — ADR NOT REQUIRED.**

The decision removes a non-required component and creates no stable physical, electrical or runtime dependency. A future proposal that installs, connects, powers or reserves capability for audio must reevaluate ADR necessity at that time.

No ADR number is allocated by IHAP-48.

---

## Downstream contract review

| Task | Accepted IHAP-48 input |
|---|---|
| IHAP-43 | GY-MAX4466 removed from reference MVP; FUTURE inventory; ADR not required |
| IHAP-49 | Audio load excluded from reference MVP power budget |
| IHAP-50 | No ADC/GPIO/wiring/passive allocation for audio |
| IHAP-51 | No microphone aperture/mounting/internal-volume requirement |
| IHAP-17 | Replace provisional `EDGE_INSTALLED_DISABLED` with FUTURE / inventory-only; reference quantity `0` |

These are handoffs. PR #32 does not modify the owner branches or implementation artifacts of those tasks.

---

## Pre-existing observation — not introduced by IHAP-48

Current `docs/product/product-vision.md` and ADR-0004 include the accepted local status display, while the protected-MVP list inside `docs/governance/source-of-truth.md` still reflects the older four-signal list and omits the display.

This divergence predates PR #32, does not affect the audio exclusion decision, and is intentionally not remediated inside IHAP-48 to avoid unrelated scope expansion. It should be corrected by separate source-of-truth maintenance.

This observation is not evidence against the IHAP-48 disposition and does not authorize any change to IHAP-46, IHAP-47 or IHAP-52.

---

## Completion recommendation

**PASS — recommend merge and IHAP-48 completion.**

Completion boundary:

```text
owned_inventory              = YES
reference_physical_presence  = NO
electrical_connection        = NO
powered                      = NO
firmware_access              = NO
mvp_audio_capability         = NO
future_audio                 = separate approval required
ADR_required                 = NO
```

No additional hardware run or runtime implementation is required for IHAP-48.
