pianic2/homeedge-ai-platform/docs/evidence/IHAP-52/summaries/pi4b-20260905T111348Z-summary.md

# IHAP-52 Physical Validation — Run pi4b-20260905T111348Z

**Task:** IHAP-52  
**ADR:** ADR-0006 — MVP Central Node Hardware Profile (`Proposed`)  
**Result:** FAIL — cooling configuration not yet accepted

## Sanitized configuration

- Raspberry Pi 4 Model B Rev 1.4
- ARM64 / `aarch64`
- 4 logical CPUs
- 8,199,639,040 bytes RAM
- Raspberry Pi OS Lite 64-bit selected in Raspberry Pi Imager
- runtime base OS: Debian GNU/Linux 13 (trixie)
- root filesystem: 30,825,431,040 bytes
- microSD: nominal 32 GB, application class A1
- PSU: 5.1 V / 3 A
- case installed
- heatsink installed
- fan absent
- approximate ambient temperature from operator setup: 28 °C

## Automated gate result

| Gate | Result |
|---|---|
| architecture | PASS |
| logical_cpus | PASS |
| ram | PASS |
| storage_capacity | PASS |
| wifi | PASS |
| repository_commit_recorded | PASS |
| repository_clean | PASS |
| pi4_model | PASS |
| pi4_aarch64 | PASS |
| vcgencmd_available | PASS |
| clean_throttle_history_before_run | PASS |
| manual_sd_application_class_supported | PASS |
| manual_rpios_lite64_confirmed | PASS |
| manual_psu_rating_parseable | PASS |
| manual_psu_supported_for_pi4 | PASS |
| storage_integrity | PASS |
| stress_workers | PASS |
| boot_stability | PASS |
| no_oom_pattern | PASS |
| vcgencmd_after_available | PASS |
| no_pi_throttle_or_undervoltage | **FAIL** |

Overall gate: **FAIL**.

## Thermal observation

Maximum CPU temperature observed during the 300-second bounded CPU stress was **84.724 °C**.

Raspberry Pi documentation states that the Arm cores are progressively throttled in the 80–85 °C range, with thermal control reducing frequency as the device approaches the thermal limit. Therefore this run is strongly consistent with a **thermal throttle event**.

The v5 summary did not expose the final `vcgencmd get_throttled` bitmask separately from the combined `no_pi_throttle_or_undervoltage` gate. For strict evidence hygiene, the exact cause is not promoted from correlation to confirmed bit-level classification in this record.

The harness has subsequently been remediated to sample/decode `get_throttled` during stress and to separate undervoltage from frequency-cap/throttle diagnostics.

## Disposition

This run does **not** reject:

- Raspberry Pi 4 Model B as the reference candidate;
- the owned A1 microSD;
- Raspberry Pi OS Lite 64-bit;
- the 5.1 V / 3 A PSU;
- storage integrity or basic resource stability.

It rejects only the tested **passive cooling configuration** (`case + heatsink, no fan`) for the current bounded 300-second stress acceptance envelope.

Next candidate configuration: same hardware/software/storage/PSU, with improved airflow / fan enabled and exact cooling setup recorded.

Because `vcgencmd` historical flags persist for the current boot, the next acceptance run must start after a reboot with a clean pre-flight throttle history.

## Remaining boundaries

Final application workload sufficiency, microSD endurance/retention and AI acceleration remain `[UNVALIDATED]`.
