pianic2/homeedge-ai-platform/docs/evidence/IHAP-52/summaries/pi4b-20260905T112848Z-summary.md

# IHAP-52 — Sanitized Physical Validation Summary

**Run ID:** `pi4b-20260905T112848Z`  
**Date:** 2026-09-05  
**Profile:** `pi4-reference`  
**Disposition:** **PASS**

## Tested configuration

- Raspberry Pi 4 Model B Rev 1.4
- Raspberry Pi OS Lite 64-bit; runtime base `Debian GNU/Linux 13 (trixie)`
- `aarch64`
- 4 logical CPUs
- 8,199,639,040 bytes RAM reported
- nominal 32 GB A1 microSD
- 30,825,431,040-byte root filesystem
- on-board Wi-Fi
- 5.1 V / 3 A PSU
- case installed
- heatsink installed
- **fan installed/enabled**

## Result

All reported gates passed:

- architecture: PASS
- logical CPUs: PASS
- RAM: PASS
- storage capacity: PASS
- Wi-Fi: PASS
- repository commit recorded: PASS
- repository clean: PASS
- Pi 4 model: PASS
- Pi 4 AArch64: PASS
- `vcgencmd` available: PASS
- clean throttle history before run: PASS
- A1/A2 application-class policy: PASS
- Raspberry Pi OS Lite 64-bit operator confirmation: PASS
- PSU parse/policy gates: PASS
- deterministic storage integrity: PASS
- stress workers: PASS
- boot stability: PASS
- no OOM pattern: PASS
- post-run `vcgencmd`: PASS
- no Pi undervoltage: PASS
- no Pi frequency cap or throttling: PASS
- no Pi soft-temperature limit: PASS

Maximum observed CPU temperature: **64.757 °C**.

Post-run Pi throttle word: **`0x0 (none)`**.

Overall gate: **PASS**.

## Comparison with passive-cooling run

The immediately preceding full bounded run `pi4b-20260905T111348Z` used the same Raspberry Pi 4 reference platform, A1 storage and 5.1 V / 3 A PSU but had no fan. It reached 84.724 °C and failed the combined Pi throttle/undervoltage gate.

This successful run therefore validates the **fan-enabled cooling configuration for the tested reference enclosure and 300-second bounded stress envelope**. It does not establish a universal requirement for active cooling on all equivalent central-node hardware; equivalent cooling solutions remain acceptable when they pass the same validation gates.

## Evidence boundary

This run validates only the bounded IHAP-52 hardware/resource envelope. The following remain `[UNVALIDATED]`:

- final HomeEdge application workload sufficiency;
- microSD endurance and retention sizing;
- Docker/container behavior;
- database behavior;
- AI acceleration/performance.

Raw local run output is intentionally not committed. This summary excludes credentials, SSID, private IP, MAC, hostname and username.
