pianic2/homeedge-ai-platform/docs/evidence/IHAP-45/summaries/stability-IHAP45-STABILITY-S2.summary.md

# IHAP-45 Functional Stability Summary — IHAP45-STABILITY-S2

**Configuration:** `S2-board-bme280`  
**Status:** `PASSED`  
**Scope:** functional stability only; no quantitative power characterization

## Aggregate result

| Check | Result |
|---|---:|
| Qualification duration | 300.0 s |
| Completed window | true |
| Boot records | 1 |
| Brownout events | 0 |
| USB disconnects after start | 0 |
| Valid sample records | 60 |

## Errors

- none

## Warnings

- none

## Evidence boundary

The serial log and individual samples remain local and are not included in the repository. This file was produced from allow-listed aggregate fields by `host/ihap45_publish.py`.
