pianic2/homeedge-ai-platform/docs/evidence/IHAP-53/final-review-summary.md

# IHAP-53 Final Specialist Review Summary

**Issue:** IHAP-53 — Local Display Decision — 0.96-inch OLED vs No Display  
**ADR:** [`ADR-0004 — Local Status Display`](../../adr/ADR-0004-local-status-display.md)  
**PR:** #31  
**Review date:** 2026-08-31  
**Reviewed physical run:** `IHAP53-DISPLAY-01`  
**Overall advisory result:** **PASS — no BLOCKER or MAJOR finding remains on the IHAP-53 branch**  
**Project Owner decision:** **ADR-0004 Accepted on 2026-08-31**.

## Review basis

The final review covers:

- `docs/adr/ADR-0004-local-status-display.md`;
- `docs/adr/README.md`;
- `docs/evidence/IHAP-53/README.md`;
- `docs/evidence/IHAP-53/publication-guide.md`;
- `docs/evidence/IHAP-53/replacement-sourcing.md`;
- `docs/evidence/IHAP-53/IHAP53-DISPLAY-01/run-record.md`;
- the three sanitized evidence PNG files;
- `tools/hardware-validation/ihap-53-local-display/`;
- Jira IHAP-53 decision and claim boundaries;
- the Product Vision controlled update authorized by ADR acceptance.

Raw `serial.log` remains local laboratory evidence by policy. The reviewed run record contains the claim-relevant facts, while the unchanged raw log remains retained locally for audit/re-review.

---

## 1. Architecture Regression Reviewer — PASS

- One stable decision: the reference MVP includes a compact read-only local status display.
- ADR-0001 compute scope is not reopened.
- DHT11 remains independent; BME280 I2C sharing remains subject to final IHAP-50 integration.
- Validation pins `GPIO5/GPIO6` are not promoted to final product pinout.
- Quantitative power, enclosure mechanics and definitive BOM remain with IHAP-49, IHAP-51 and IHAP-17.
- Product Vision update is limited to the accepted MVP capability and does not claim completed final firmware integration.

## 2. Hardware Compatibility Reviewer — PASS

- Tested specimen marking: `GME12864-11-12-13 V3.22`; observed blue OLED.
- Physical evidence supports 3.3 V operation, I2C `0x3C`, 128×64 rendering, repeated updates and controlled reinitialization.
- Claim is correctly limited to **SSD1306 command/profile compatibility**, not independent identification of the controller die.
- `0x3D`, replacement compatibility, pull-ups, final wiring and mechanical interchangeability remain outside the physical evidence.

## 3. Testing & Evidence Reviewer — PASS

- Short functional gate: PASS.
- Highest accepted pre-reset heartbeat: `elapsed_s=3622` (`>=3600`).
- Controlled reboot/reinitialization: PASS.
- Operator visual evidence covers full-on, full-off, checkerboard, readable `HOMEEDGE / IHAP53`, correct orientation and moving stability marker.
- Published evidence contains reviewed run record, front text-card, rear PCB and annotated wiring photographs.
- Host-side monitor disconnection occurred after the required reboot/re-init evidence was already captured and is non-invalidating.
- No additional hardware run is required.

## 4. Cost Governance Reviewer — PASS

- Owned inventory is not treated as zero replication cost.
- Replacement sourcing remains a dated, non-guaranteed market snapshot.
- IHAP-17 receives the accepted display profile/tested-reference/cost handoff after ADR acceptance.
- No unsupported lifetime, power-cost or procurement-reproducibility claim is introduced.

## 5. Source of Truth Guardian — PASS

- GitHub remains canonical for ADR content and technical evidence.
- Jira retains workflow state, Project Owner decision authority and evidence links.
- Confluence remains stakeholder summary/navigation only.
- IHAP-53 uses ADR-0004 consistently and does not modify IHAP-52.
- Acceptance is recorded only after physical PASS, final specialist review and explicit Project Owner approval.

## 6. Security & Privacy Reviewer — PASS

- Display content remains current room-level telemetry only.
- Identity, person tracking, behavioral/occupancy history, SSID, credentials, alarm/security semantics and access-control claims remain excluded.
- IP address remains maintenance-only when needed, not normal-dashboard content.
- No production-ready, security-grade, alarm-grade, antifurto, access-control, safety-critical or certification claim is introduced.

## 7. Stakeholder Clarity Reviewer — PASS

- Functional requirement, reusable profile and tested owned specimen are clearly separated.
- Physical PASS and its limitations are visible without requiring raw serial output.
- 4xy/5xy codes are HomeEdge device codes, not HTTP response statuses.
- Follow-up ownership for power, interconnect, enclosure and BOM remains explicit.
- ADR-0004 is now unambiguously **Accepted** by the Project Owner.

---

## Resolved closure findings

| Finding | Resolution |
|---|---|
| Evidence package absent from remote branch | Resolved — published under `docs/evidence/IHAP-53/IHAP53-DISPLAY-01/` |
| ADR numbering collision from IHAP-53 branch | Resolved — IHAP-53 renumbered to ADR-0004; IHAP-52 untouched |
| Run-record rear-photo contradiction | Resolved |
| `SSD1306 validated` overclaim | Resolved — narrowed to SSD1306 command/profile compatibility |
| Evidence README pre-validation state | Resolved |
| ADR/index/PR body pre-validation state | Resolved |
| Required specialist review not recorded | Resolved |
| Project Owner acceptance pending | Resolved — ADR-0004 accepted 2026-08-31 |
| Product Vision authorization pending | Resolved — controlled update authorized by acceptance |

## Closure conclusion

No technical or documentation remediation remains on the IHAP-53 branch.

ADR-0004 is **Accepted**. Remaining work is closure synchronization only: finalize the Product Vision change on this branch, finalize/merge PR #31, transition Jira IHAP-53, and update Confluence stakeholder navigation. This review does not expand IHAP-53 into final firmware, power, pinout, enclosure or BOM implementation.
