pianic2/homeedge-ai-platform/docs/evidence/IHAP-47/IHAP47-MC38-A-01/photo-mounting.jpg

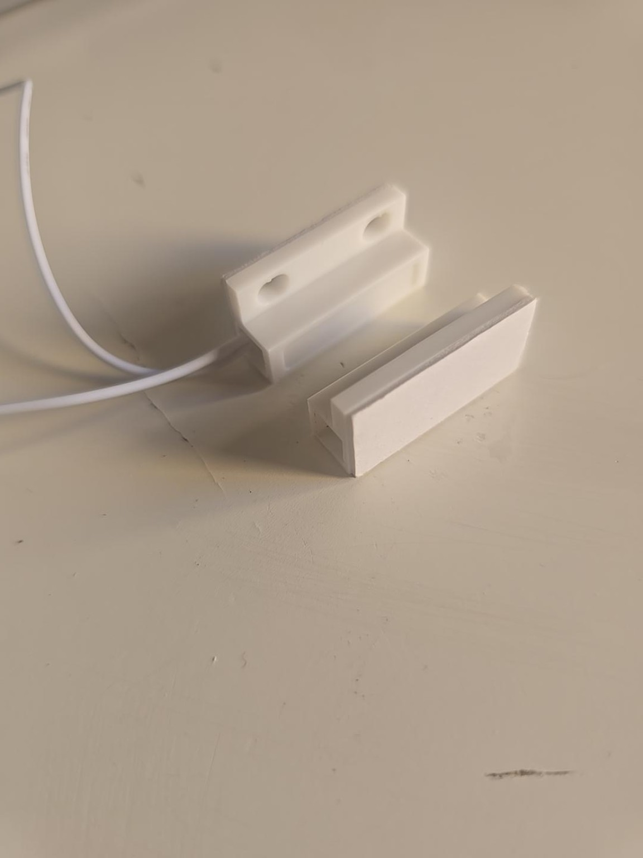
docs/evidence/IHAP-47/IHAP47-MC38-A-01/photo-mounting.jpg
