pianic2/homeedge-ai-platform/docs/evidence/IHAP-53/IHAP53-DISPLAY-01/photo-rear-marking.png

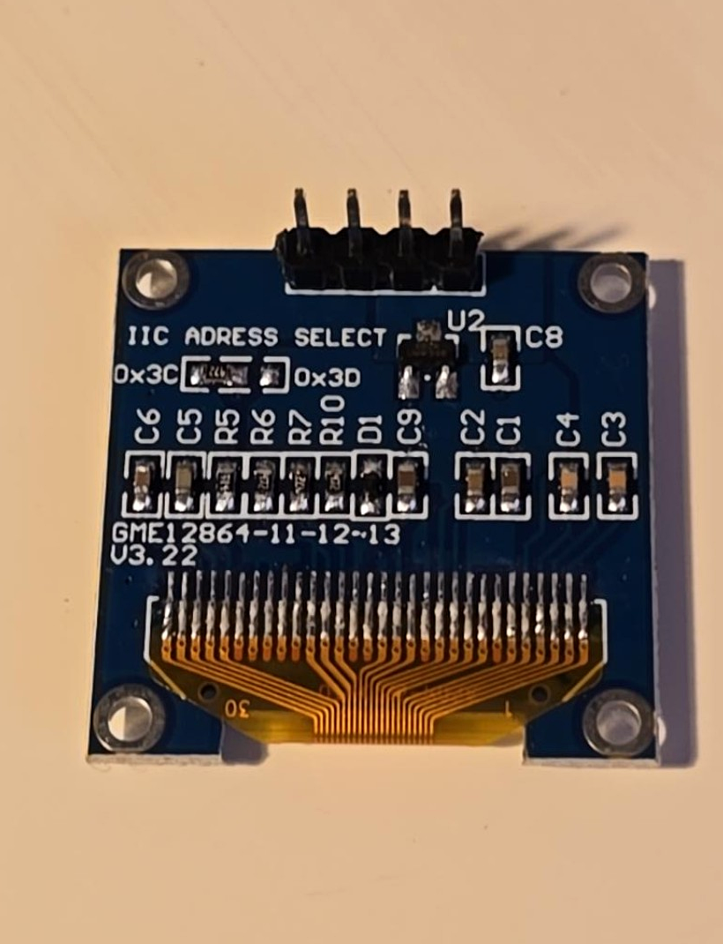
docs/evidence/IHAP-53/IHAP53-DISPLAY-01/photo-rear-marking.png
