pianic2/homeedge-ai-platform/docs/evidence/IHAP-53/IHAP53-DISPLAY-01/photo-wiring-annotated.png

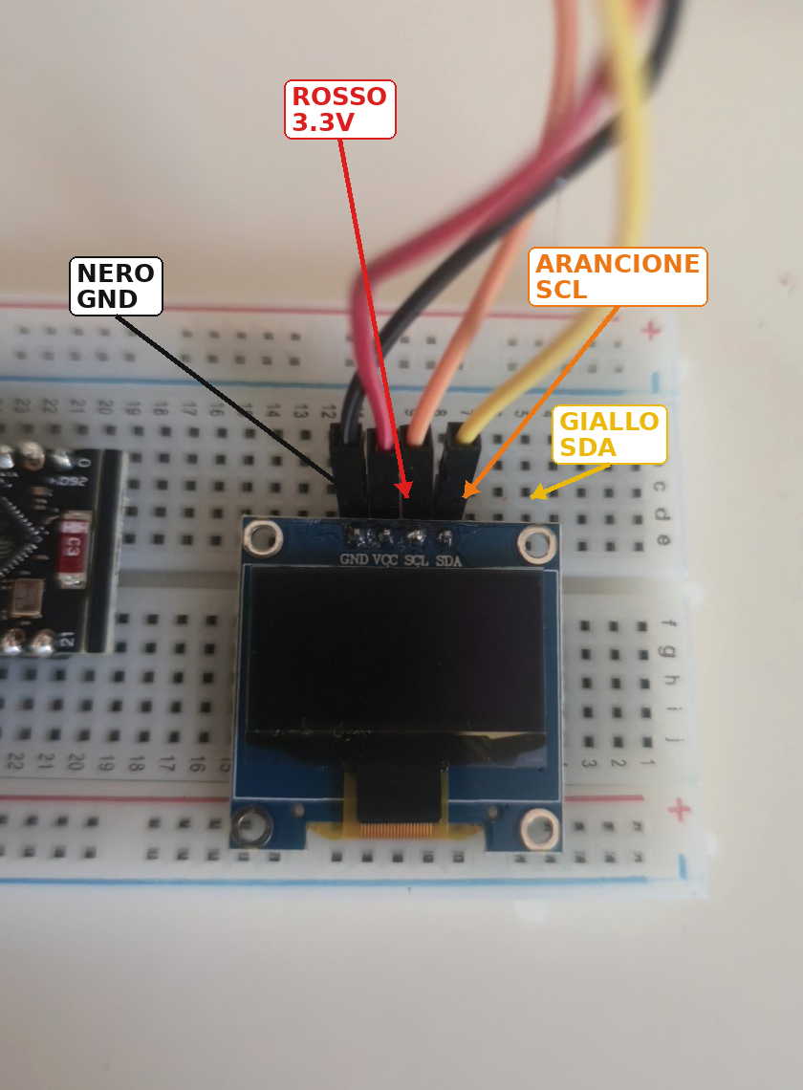
docs/evidence/IHAP-53/IHAP53-DISPLAY-01/photo-wiring-annotated.png
