pianic2/homeedge-ai-platform/hardware/edge-mainboard/homeedge-edge-mainboard.kicad_sch

## KiCad design hardware/edge-mainboard/homeedge-edge-mainboard.kicad_sch (2026-09-21)

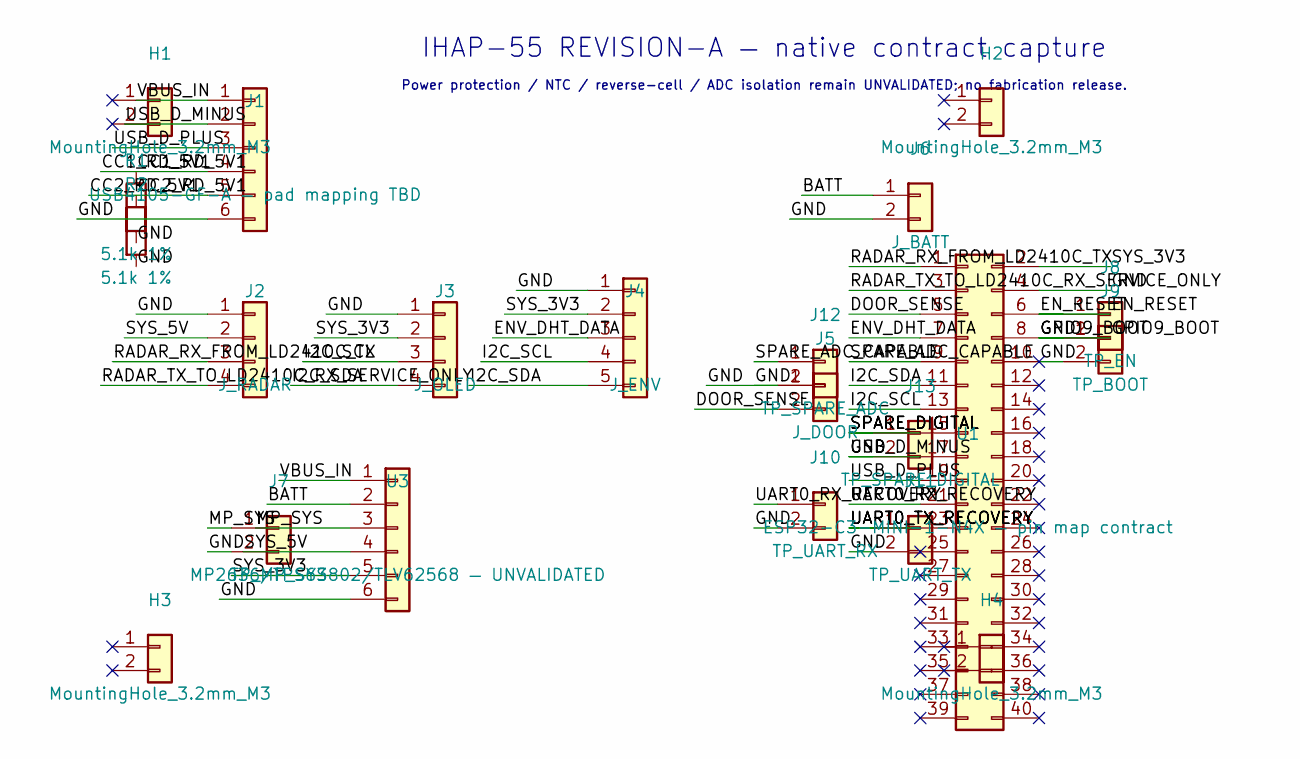
[picture p10: schematic homeedge-edge-mainboard.kicad_sch]

Parts:
H1, H2, H3, H4: MountingHole_3.2mm_M3
J1: USB4105-GF-A — pad mapping TBD
J2: J_RADAR
J3: J_OLED
J4: J_ENV
J5: J_DOOR
J6: J_BATT
J7: TP_MP_SYS
J8: TP_EN
J9: TP_BOOT
J10: TP_UART_RX
J11: TP_UART_TX
J12: TP_SPARE_ADC
J13: TP_SPARE_DIGITAL
R1, R2: 5.1k 1%
U1: ESP32-C3-MINI-1-N4X — pin map contract
U3: MP2636/TPS63802/TLV62568 — UNVALIDATED

Connections:
BATT: J6.1, U3.2
CC1_RD_5V1: J1.4, R1.1
CC2_RD_5V1: J1.5, R2.1
DOOR_SENSE: J5.2, U1.5
ENV_DHT_DATA: J4.3, U1.7
EN_RESET: J8.1, U1.6
GND: J1.2, J1.6, J2.1, J3.1, J4.1, J5.1, J6.2, J7.2, J8.2, J9.1, J9.2, J10.2, J11.2, J12.2, J13.2, R1.2, R2.2, U1.4, U1.8, U1.10, U1.17, U3.6
I2C_SCL: J3.3, J4.4, U1.13
I2C_SDA: J3.4, J4.5, U1.11
MP_SYS: J7.1, U3.3
RADAR_RX_FROM_LD2410C_TX: J2.3, U1.1
RADAR_TX_TO_LD2410C_RX_SERVICE_ONLY: J2.4, U1.3
SPARE_ADC_CAPABLE: J12.1, U1.9
SPARE_DIGITAL: J13.1, U1.15
SYS_3V3: J3.2, J4.2, U1.2, U3.5
SYS_5V: J2.2, U3.4
UART0_RX_RECOVERY: J10.1, U1.21
UART0_TX_RECOVERY: J11.1, U1.23
USB_D_PLUS: J1.3, U1.19
VBUS_IN: J1.1, U3.1

Notes on the sheet:
IHAP-55 REVISION-A — native contract capture
Power protection / NTC / reverse-cell / ADC isolation remain UNVALIDATED; no fabrication release.
