pianic2/homeedge-ai-platform/tools/hardware-validation/ihap-46-presence-sensor/tests/test_guided_run.py

from __future__ import annotations

import importlib.util
import io
import json
from pathlib import Path
from types import SimpleNamespace
import sys
import tempfile
import unittest
from contextlib import redirect_stdout
from unittest import mock

ROOT = Path(__file__).resolve().parents[1]
HOST = ROOT / "host"
if str(HOST) not in sys.path:
    sys.path.insert(0, str(HOST))

import ihap46  # type: ignore

SPEC = importlib.util.spec_from_file_location("guided_run", HOST / "guided_run.py")
assert SPEC and SPEC.loader
guided_run = importlib.util.module_from_spec(SPEC)
SPEC.loader.exec_module(guided_run)


class GuidedRunTests(unittest.TestCase):
    def setUp(self) -> None:
        self.plan = {
            "schema_version": "1.0.0",
            "issue": "IHAP-46",
            "scenarios": [
                {
                    "id": "REQUIRED",
                    "title": "Required scenario",
                    "required": True,
                    "duration_s": 65,
                    "repetitions": 2,
                    "ground_truth": "empty",
                    "door_state": "closed",
                    "expected": {
                        "ld2410c_uart": {"max_presence_ratio": 0.1},
                        "pir_out": {"max_presence_ratio": 0.1},
                    },
                },
                {
                    "id": "OPTIONAL",
                    "title": "Optional scenario",
                    "required": False,
                    "duration_s": 30,
                    "repetitions": 1,
                    "ground_truth": "adjacent_activity",
                    "door_state": "closed",
                    "expected": {
                        "ld2410c_uart": {"max_presence_ratio": 0.1}
                    },
                },
            ],
        }
        self.environment = {
            "schema_version": "1.0.0",
            "issue": "IHAP-46",
            "profile_id": "ROOM-5X5-DOOR-CORNER-ABOVE-DOOR",
            "description": "Reference setup",
            "defaults": {
                "room_id": "ROOM-5X5-DOOR-CORNER-01",
                "room_shape": "square",
                "room_width_m": 5.0,
                "room_depth_m": 5.0,
                "door_location": "near one corner",
                "mount_height_cm": 200.0,
                "mount_position": "above the door",
                "mount_orientation": "antenna side facing into the room",
                "room_notes": "reference notes",
            },
            "reference_test_positions": {
                "room_center": "2.50 m from each wall"
            },
            "override_rule": "May be corrected.",
        }

    def test_default_selection_excludes_optional(self) -> None:
        selected = guided_run.select_scenarios(self.plan, [], False)
        self.assertEqual(["REQUIRED"], [item["id"] for item in selected])

    def test_explicit_selection_preserves_requested_order(self) -> None:
        selected = guided_run.select_scenarios(
            self.plan, ["OPTIONAL", "REQUIRED"], False
        )
        self.assertEqual(["OPTIONAL", "REQUIRED"], [item["id"] for item in selected])

    def test_effective_plan_contains_only_selected_sensor(self) -> None:
        selected = guided_run.select_scenarios(self.plan, ["REQUIRED"], False)
        effective = guided_run.build_effective_plan(
            self.plan, selected, ["ld2410c_uart"]
        )
        self.assertEqual(
            ["ld2410c_uart"],
            list(effective["scenarios"][0]["expected"]),
        )
        self.assertEqual(["ld2410c_uart"], effective["selected_sensor_channels"])

    def test_operator_actions_require_human_instructions(self) -> None:
        payload = {
            "schema_version": "1.0.0",
            "issue": "IHAP-46",
            "actions": {
                "REQUIRED": {
                    "purpose": "purpose",
                    "start_action": "ACT",
                    "setup": ["setup"],
                    "during_capture": ["act"],
                    "invalid_if": ["invalid"],
                },
                "OPTIONAL": {
                    "purpose": "purpose",
                    "start_action": "ACT",
                    "setup": ["setup"],
                    "during_capture": ["act"],
                    "invalid_if": ["invalid"],
                },
            },
        }
        with tempfile.TemporaryDirectory() as directory:
            path = Path(directory) / "actions.json"
            path.write_text(json.dumps(payload), encoding="utf-8")
            loaded = guided_run.load_actions(path, self.plan)
        self.assertEqual(
            "act", loaded["actions"]["REQUIRED"]["during_capture"][0]
        )

    def test_environment_profile_requires_reference_geometry(self) -> None:
        with tempfile.TemporaryDirectory() as directory:
            path = Path(directory) / "environment.json"
            path.write_text(json.dumps(self.environment), encoding="utf-8")
            loaded = guided_run.load_environment(path)
        self.assertEqual(5.0, loaded["defaults"]["room_width_m"])
        self.assertEqual(200.0, loaded["defaults"]["mount_height_cm"])

    def test_environment_defaults_are_overridable(self) -> None:
        args = SimpleNamespace(
            room_id=None,
            room_width_m=4.5,
            room_depth_m=None,
            door_location=None,
            mount_height_cm=210.0,
            mount_orientation=None,
            mount_position=None,
            room_notes="corrected notes",
        )
        effective = guided_run.effective_environment(self.environment, args)
        self.assertEqual(4.5, effective["values"]["room_width_m"])
        self.assertEqual(5.0, effective["values"]["room_depth_m"])
        self.assertEqual(210.0, effective["values"]["mount_height_cm"])
        self.assertEqual("corrected notes", effective["values"]["room_notes"])

    def test_sensor_specific_scenario_is_skipped_when_channel_missing(self) -> None:
        actions = {
            "actions": {
                "REQUIRED": {},
                "OPTIONAL": {
                    "required_sensor_channels": ["ld2410c_uart", "ld2410c_out"]
                },
            }
        }
        selected = guided_run.filter_scenarios_for_sensors(
            self.plan["scenarios"], actions, ["ld2410c_uart"], []
        )
        self.assertEqual(["REQUIRED"], [item["id"] for item in selected])

    def test_scenario_card_is_actionable_and_english(self) -> None:
        action = {
            "purpose": "Verify an empty room.",
            "start_action": "MAINTAIN EMPTY ROOM CONDITIONS",
            "setup": ["Close the door."],
            "during_capture": ["Keep the room empty."],
            "invalid_if": ["A person enters."],
        }
        card = guided_run.scenario_card(self.plan["scenarios"][0], action, 1)
        self.assertIn("Duration: 01:05", card)
        self.assertIn("START ACTION", card)
        self.assertIn("MAINTAIN EMPTY ROOM CONDITIONS", card)
        self.assertIn("A person enters.", card)

    def test_scenario_card_contains_operator_sections_and_start_action(self) -> None:
        action = {
            "purpose": "Measure entry.",
            "start_action": "ENTER THE ROOM",
            "setup": ["Stand outside."],
            "during_capture": ["Reach the endpoint."],
            "invalid_if": ["You enter early."],
        }
        card = guided_run.scenario_card(
            {
                **self.plan["scenarios"][0],
                "id": "ENTER_ROOM",
                "title": "Enter",
                "door_state": "open",
            },
            action,
            1,
        )
        for section in ("IHAP-46 PHYSICAL VALIDATION", "PURPOSE", "SETUP", "INVALID IF", "START ACTION"):
            self.assertIn(section, card)
        self.assertIn(">>> ENTER THE ROOM <<<", card)

    def test_canonical_actions_have_start_instructions_for_every_scenario(self) -> None:
        plan_path = ROOT / "config" / "test-plan.json"
        actions_path = ROOT / "config" / "operator-actions.json"
        plan = ihap46.load_json(plan_path)
        actions = guided_run.load_actions(actions_path, plan)
        self.assertEqual(
            {scenario["id"] for scenario in plan["scenarios"]},
            set(actions["actions"]),
        )
        self.assertTrue(
            all(
                isinstance(action.get("start_action"), str)
                and action["start_action"].strip()
                for action in actions["actions"].values()
            )
        )

    def test_start_signal_event_and_marker_share_timestamp(self) -> None:
        scenario = {
            "id": "ENTER_ROOM",
            "ground_truth": "present_moving",
            "door_state": "open",
        }
        action = {"start_action": "ENTER THE ROOM"}
        with tempfile.TemporaryDirectory() as directory:
            run_dir = Path(directory)
            with mock.patch.object(ihap46, "epoch_ms", return_value=1234):
                guided_run.emit_start_signal(
                    run_dir, scenario, action, 1, "test marker"
                )
            events = list(ihap46.iter_jsonl(run_dir / "capture-events.jsonl"))
            markers = list(ihap46.iter_jsonl(run_dir / "marks.jsonl"))

        self.assertEqual(["operator_start_signal_emitted"], [event["event"] for event in events])
        self.assertEqual(1234, events[0]["at_epoch_ms"])
        self.assertEqual(1234, markers[0]["at_epoch_ms"])
        self.assertEqual("ENTER THE ROOM", events[0]["action"])

    def test_operator_guidance_flushes_countdown_and_capture_instructions(self) -> None:
        output = io.StringIO()
        with mock.patch.object(guided_run.time, "sleep"):
            with redirect_stdout(output):
                guided_run.action_countdown()
                guided_run.print_recording_guidance(
                    {"during_capture": ["Walk normally.", "Remain in the room."]}
                )
        text = output.getvalue()
        self.assertIn("[ACTION COUNTDOWN]", text)
        self.assertIn("Do NOT perform the action yet.", text)
        self.assertIn("5...", text)
        self.assertIn("[RECORDING ACTIVE]", text)
        self.assertIn("- Walk normally.", text)
        self.assertIn("Do not stop until the runner reports REPETITION COMPLETE.", text)

    def test_room_empty_start_action_does_not_instruct_entry(self) -> None:
        actions = guided_run.load_actions(
            ROOT / "config" / "operator-actions.json",
            ihap46.load_json(ROOT / "config" / "test-plan.json"),
        )
        action = actions["actions"]["ROOM_EMPTY_BASELINE"]
        self.assertNotIn("ENTER", action["start_action"])
        self.assertNotIn("LEAVE", action["start_action"])

    def test_exit_clear_makes_latency_origin_and_immediate_action_explicit(self) -> None:
        actions = guided_run.load_actions(
            ROOT / "config" / "operator-actions.json",
            ihap46.load_json(ROOT / "config" / "test-plan.json"),
        )
        action = actions["actions"]["EXIT_CLEAR"]
        combined = " ".join(
            [
                action["purpose"],
                action["start_action"],
                *action["during_capture"],
                *action["invalid_if"],
            ]
        ).lower()
        self.assertIn("start now", combined)
        self.assertIn("immediately", combined)
        self.assertIn("clock", combined)
        self.assertIn("delay", combined)

    def test_preflight_accepts_reconnect_with_valid_uart_without_boot(self) -> None:
        with tempfile.TemporaryDirectory() as directory:
            run_dir = Path(directory)
            ihap46.append_jsonl(
                run_dir / "records.jsonl",
                {
                    "received_at_epoch_ms": 1200,
                    "source": {
                        "record_type": "sample",
                        "ld2410c": {"uart_frame_valid": True},
                    },
                },
            )
            ihap46.append_jsonl(
                run_dir / "capture-events.jsonl",
                {
                    "at_epoch_ms": 1050,
                    "event": "serial_disconnected",
                },
            )
            ihap46.append_jsonl(
                run_dir / "capture-events.jsonl",
                {
                    "at_epoch_ms": 1100,
                    "event": "serial_connected",
                },
            )
            snapshot = guided_run.preflight_snapshot(
                run_dir, 1000, ["ld2410c_uart"]
            )

        self.assertEqual("PASS", snapshot["status"])
        self.assertEqual(0, snapshot["fresh_boot_count"])
        self.assertEqual(1, snapshot["fresh_valid_uart_count"])
        self.assertTrue(snapshot["serial_reconnect_after_disconnect"])

    def test_preflight_accepts_boot_with_valid_uart_without_disconnect(self) -> None:
        with tempfile.TemporaryDirectory() as directory:
            run_dir = Path(directory)
            ihap46.append_jsonl(
                run_dir / "records.jsonl",
                {
                    "received_at_epoch_ms": 1100,
                    "source": {"record_type": "boot"},
                },
            )
            ihap46.append_jsonl(
                run_dir / "records.jsonl",
                {
                    "received_at_epoch_ms": 1200,
                    "source": {
                        "record_type": "sample",
                        "ld2410c": {"uart_frame_valid": True},
                    },
                },
            )
            snapshot = guided_run.preflight_snapshot(
                run_dir, 1000, ["ld2410c_uart"]
            )

        self.assertEqual("PASS", snapshot["status"])
        self.assertEqual(1, snapshot["fresh_boot_count"])
        self.assertFalse(snapshot["serial_reconnect_after_disconnect"])

    def test_preflight_ignores_valid_samples_before_start(self) -> None:
        with tempfile.TemporaryDirectory() as directory:
            run_dir = Path(directory)
            ihap46.append_jsonl(
                run_dir / "records.jsonl",
                {
                    "received_at_epoch_ms": 900,
                    "source": {
                        "record_type": "sample",
                        "ld2410c": {"uart_frame_valid": True},
                    },
                },
            )
            snapshot = guided_run.preflight_snapshot(
                run_dir, 1000, ["ld2410c_uart"]
            )

        self.assertEqual("WAIT", snapshot["status"])
        self.assertEqual(0, snapshot["fresh_sample_count"])


if __name__ == "__main__":
    unittest.main()
